claudioarena/EQMOD_DIRECT_Isolated/images/IMG_20201231_185849.jpg

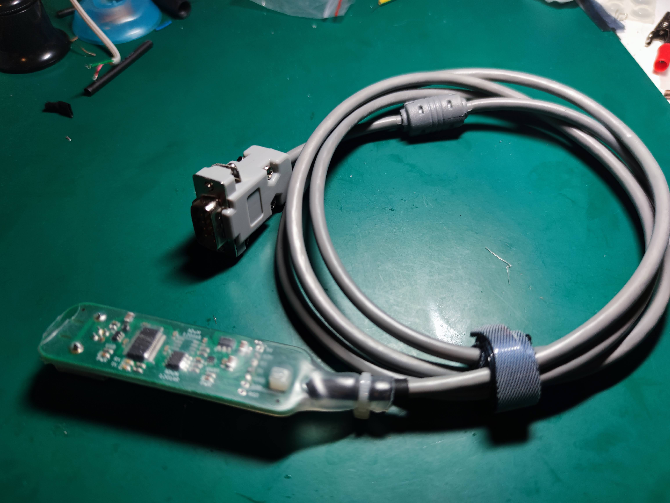
images/IMG_20201231_185849.jpg
