claudioarena/EQMOD_DIRECT_Isolated/images/IMG_20201231_185941.jpg

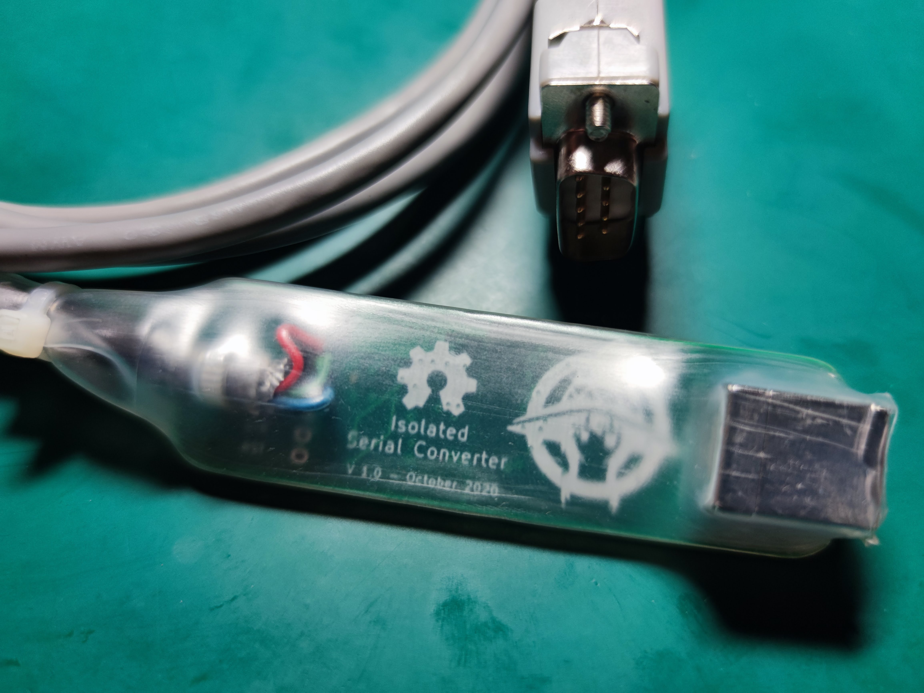
images/IMG_20201231_185941.jpg
