claudioarena/EQMOD_DIRECT_Isolated/images/IMG_20201231_190030.jpg

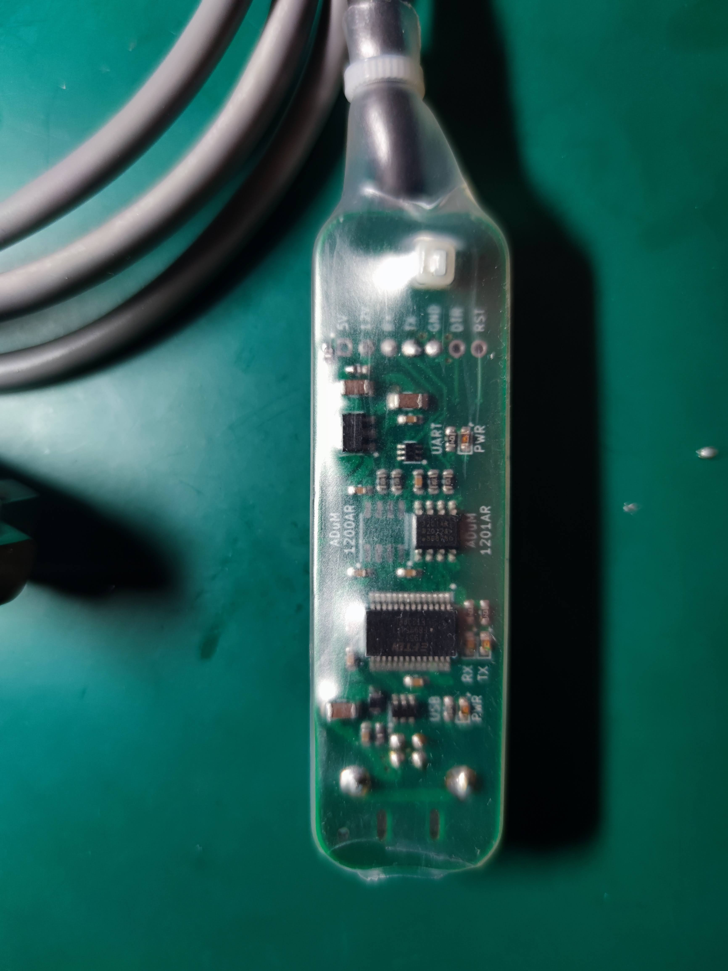
images/IMG_20201231_190030.jpg
